thingsat/tinygs_2g4station/Firmware/Arduino/GroveTemperatureHumidity_TH02/README.md

# Grove Temperature&Humidity TH02

https://wiki.seeedstudio.com/Grove-TemptureAndHumidity_Sensor-High-Accuracy_AndMini-v1.0/

Step 1. Install the `Grove Temperature&Humidity TH02` library with `Tools > Manage Library ...`.

Step 2. Open, Build and Load the sketch `File > Examples > Grove Temper Humidity_TH02 > TH02_demo`

Step 3. Open the serial monitor with baudrate 9600 baud
