thingsat/tinygs_2g4station/Firmware/Arduino/RTC_DS1307/README.md

# RTC DS1307
https://www.arduino.cc/reference/en/libraries/ds1307rtc/
