thingsat/tinygs_2g4station/Firmware/Arduino/RTC_DS3231/README.md

# RTC DS3231
https://www.arduino.cc/reference/en/libraries/ds3231/
