thingsat/tinygs_2g4station/Firmware/Arduino/ADC_23_Click/README.md

# ADC 23 Click (MIKROE-5861)

https://www.mikroe.com/adc-23-click
