thingsat/tinygs_2g4station/Firmware/Arduino/ADC_8_Click/README.md

# ADC 8 Click (MIKROE-3394)

https://www.mikroe.com/adc-8-click

ADC 8 Click is a high precision, low-power, 16-bit analog-to-digital converter (ADC), based around the ADS1115 IC. It is capable of sampling signals on four single-ended or two differential input channels.
