thingsat/tinygs_2g4station/Firmware/Arduino/CAN/README.md

# CAN Bus

https://www.mikroe.com/click/interface/can
