thingsat/tinygs_2g4station/Firmware/Arduino/RS485_5_Click/README.md

# RS485 5 Click

The RS485 5 Click is a Click board™ equipped with the MAX485, low-power, slew-rate-limited transceiver for RS-485 and RS-422 communication, from Analog Devices. This device supports half-duplex RS-485 communication and can be used as an interface between the TTL level UART and the RS485 communication bus

https://www.mikroe.com/rs485-5-click
