thingsat/tinygs_2g4station/Firmware/Arduino/X-NUCLEO-IHM02A1/README.md

# X-NUCLEO-IHM02A1 Nucleo shield for driving steppers

https://www.st.com/en/ecosystems/x-nucleo-ihm02a1.html

Two axis stepper motor driver expansion board based on the L6470 for STM32 Nucleo
