thingsat/tinygs_2g4station/Firmware/Arduino/Grove_LCD_2x16/README.md

# Grove - LCD RGB Backlight

Connect a [Grove - LCD RGB screen](https://wiki.seeedstudio.com/Grove-LCD_RGB_Backlight/) on the I2C connector.

Download and install the [LCD lib](https://codeload.github.com/Seeed-Studio/Grove_LCD_RGB_Backlight/zip/refs/heads/master).

There are 12 examples for testing with the library.

Open `Scroll` in `File > Examples > Grove_LCD_RGB_Backlight-master`.
