thingsat/tinygs_2g4station/Firmware/Arduino/Analog_Input_Joystick/README.md

# Grove Thumb Joystick

Code for reading the 2 analog inputs of the Grove Thumb Joystick. 

This code can be used for controling manually the 2 steppers of the cubesat antenna tracker.

If you use the Board_Tinygs_2.4GHz_V1, the Grove Thumb Joystick can be directly connected to IN 34/35 grove connector.
