thingsat/tinygs_2g4station/Firmware/Arduino/GroveLoRaE5/README.md

# TinyGS 2G4 avec Grove LoRa E5

La platine [Grove LoRa E5](https://wiki.seeedstudio.com/Grove_LoRa_E5_New_Version) est un modem LoRaWAN basé sur le composant STM32WL55JC1. Le modem est commandable via des commandes AT (voir la [section Bonus](#Bonus)).

Il peut être branché sur la carte TinyGS 2G4 pour ajouter la connectivité LoRaWAN sur les bandes SubGHz (eu868, eu433 ...).

## Branchement

Le modem Grove LoRa E5 peut soit être branché 
* soit sur le connecteur Grove UART de la carte TinyGS
* soit être branché sur le header 2x19 de la carte TinyGS : Le fil blanc du cable Grove doit être branché sur la broche 17 du header 2x19 et le fil jaune du cable Grove doit être branché sur la broche 16.

## Sketch Arduino sur TinyGS 2G4

Ouvrez le Sketch [GroveLoRaE5.ino](GroveLoRaE5.ino)

Configurez les constantes dans le sketch
```c
#define DEBUG_AT 1
#define SEND_PERIOD 60000
#define REJOIN_PERIOD 60000
#define CONFIRMED 1
```

## Enregistrement

Repérez et relevez le `DevEUI`, l'`AppEUI` et l'`AppKey` de la [platine Grove LoRa E5](https://wiki.seeedstudio.com/Grove_LoRa_E5_New_Version/) dans la console série du enpoint.

Enregistrez le enpoint sur un réseau LoRaWAN ([TTN](https://console.cloud.thethings.network/), [Helium](https://console.helium.com/) ou Chirpstack) en utilisant le `DevEUI`, l'`AppEUI` et l'`AppKey` relevés.

> Vous pouvez changer les valeurs d'`AppEUI` et d'`AppKey` dans le croquis.

## Ajout d'une platine avec un capteur I2C

Vous pouvez améliorer le sketch en branchant une platine avec un capteur I2C sur le connecteur Grove I2C de la carte TinyGS

Ajoutez alors un décodeur adapté lors de l'enregistrement du enpoint sur le réseau LoRaWAN choisi.

Par exemple :

```javascript
function readInt16BE (buf, offset) {
    offset = offset >>> 0
    var val = buf[offset + 1] | (buf[offset] << 8)
    return (val & 0x8000) ? val | 0xFFFF0000 : val
  }

// For Helium et TTNv2
function Decode(fPort, bytes, variables) {
    var o = {};  
    o.temperature = readInt16BE(bytes,0);
    o.humidity = readInt16BE(bytes,2);
    // ...
    return o;
}

// For Helium et TTNv2
function Decoder(bytes, fPort) {
    return Decode(fPort, bytes, undefined);
}

// For  TTNv3 TODO

```

> Pour Helium, il faut [créer une nouvelle fonction](https://console.helium.com/functions).

Faites quelques tests pour changer les valeurs du capteur ...

Regardez les messages LoRaWAN envoyés par l'endpoint lorsque la procédure d'activation OTAA a réussi.

## Références

* https://wiki.seeedstudio.com/Grove_LoRa_E5_New_Version/
* https://files.seeedstudio.com/products/317990687/res/LoRa-E5%20AT%20Command%20Specification_V1.0%20.pdf

## Bonus

### Utilisation avec un adaptateur USB Série (aka FTDI) depuis un hôte Linux/MacOS/Windows

Branchez un cable Grove femelle sur l'adapteur USB Série (`RX` sur fil jaune, `TX` sur fil blanc).

Ouvrez une console série sur le prot série avec les paramêtres `9600 8N1`.

```
AT+ID                                                                   
+INFO: Input timeout                                                            
+ID: DevAddr, 32:30:A5:01                                                       
+ID: DevEui, 2C:F7:F1:20:12:23:34:45                                            
+ID: AppEui, 80:00:00:00:00:00:00:06                                            

AT+DR=EU868
+INFO: Input timeout                                                            
+DR: EU868                                                                      
                                                                                
AT+CH=NUM,0-2
+INFO: Input timeout                                                            
+CH: NUM, 0-2                                                                   

AT+KEY=APPKEY,2B7E151628AED2A6ABF7158809CF4F3C
+INFO: Input timeout                                                            
+KEY: APPKEY 2B7E151628AED2A6ABF7158809CF4F3C                                   

AT+MODE=LWOTAA
+INFO: Input timeout                                                            
+MODE: LWOTAA                                                                   
                                                                               
AT+CLASS=A
+INFO: Input timeout                                                            
+CLASS: A                                                                       
                                                                                
AT+PORT=8
+INFO: Input timeout                                                            
+PORT: 8                                                                        
                                                                                
AT+JOIN
+INFO: Input timeout                                                            
+JOIN: Start                                                                    
+JOIN: NORMAL                                                                   
+JOIN: Join failed                                                              
+JOIN: Done                                                                     
                                                                                
AT+JOIN
+INFO: Input timeout                                                            
+JOIN: Start                                                                    
+JOIN: NORMAL                                                                   
+JOIN: Network joined                                                           
+JOIN: NetID C0002B DevAddr FC:00:AC:2C                                         
+JOIN: Done                                                                     

AT+ID
+INFO: Input timeout                                                            
+ID: DevAddr, FC:00:AC:2C                                                       
+ID: DevEui, 2C:F7:F1:20:12:23:34:45                                            
+ID: AppEui, 80:00:00:00:00:00:00:06                                            

AT+CMSGHEX=2122232421222324
+INFO: Input timeout                                                            
+CMSGHEX: Start                                                                 
+CMSGHEX: Wait ACK                                                              
+CMSGHEX: FPENDING                                                              
+CMSGHEX: ACK Received                                                          
+CMSGHEX: RXWIN1, RSSI -72, SNR 6.0                                             
+CMSGHEX: Done                                                                  
                                                                                
AT+CMSGHEX=2122232421222324
+INFO: Input timeout                                                            
+CMSGHEX: Start                                                                 
+CMSGHEX: Wait ACK                                                              
+CMSGHEX: FPENDING                                                              
+CMSGHEX: ACK Received                                                          
+CMSGHEX: RXWIN1, RSSI -72, SNR 13.0                                            
+CMSGHEX: Done                                                                  

AT+DR
+INFO: Input timeout                                                            
+DR: DR0 (ADR DR5)                                                              
+DR: EU868 DR5  SF7  BW125K                                                     
+DR: EU868 DR0  SF12 BW125K                                                     
                                                                         
AT+ADR
+INFO: Input timeout                                                            
+ADR: ON                                                                        
                                                                                
AT+POWER
+INFO: Input timeout                                                            
+POWER: 12                                                                      
                                                                                
AT+VDD
+INFO: Input timeout                                                            
+VDD: 3.27V                                                                     
                                                                                
AT+WDT
+INFO: Input timeout                                                            
+WDT: ON                                                                        
                                                                                
AT+LOG
+INFO: Input timeout                                                            
+LOG: QUIET                                                                     

AT+LOG=DEBUG
+INFO: Input timeout                                                                                            
+LOG: DEBUG                                                                                                     
                                                                                
AT+CMSGHEX=2122232421222324
+INFO: Input timeout                                                            
+LOG: DEBUG                                                                     
+LOG: DEBUG   971961 LW      MACCMD, TX, 030706FF06                             
+LOG: DEBUG   971961 LW      MACCMD, RX, 0352FF0001                             
+LOG: DEBUG   971962 LW      ch 02                                              
+LOG: DEBUG   971962 LORA    RX, 868500000, SF7, 125KHz, 24                     
                                                                                
AT+CMSGHEX=2122232421222324
+INFO: Input timeout                                                            
+LOG:  WARN   988473 LW      tx 8, 2122232421222324(8)                          
+CMSGHEX: Start                                                                 
+CMSGHEX: Wait ACK                                                              
+LOG: DEBUG   988474 LW      MACCMD, TX, 0307                                   
+LOG: DEBUG   988474 LW      ch 00                                              
+LOG: DEBUG   988474 LORA    TX, 868100000, SF7, 125KHz, 8, 12                  
+LOG: DEBUG   988475 LORA    TX, 802CAC00FC82020003070897084ED874A8279461E7AFC3 
+LOG: DEBUG   989535 LORA    RX, 868100000, SF7, 125KHz, 24                     
+LOG: DEBUG   989594 LORA    RX, 602CAC00FCA502000354FF00012067D51D, -70, 14    
+LOG: DEBUG   989595 LW      MACCMD, RX, 0354FF0001                             
+CMSGHEX: FPENDING                                                              
+CMSGHEX: ACK Received                                                          
+CMSGHEX: RXWIN1, RSSI -70, SNR 14.0                                            
+CMSGHEX: Done

AT+CMSGHEX=2122232421222324
+INFO: Input timeout
+LOG:  WARN  1049959 LW      tx 8, 2122232421222324(8)
+CMSGHEX: Start
+CMSGHEX: Wait ACK
+LOG: DEBUG  1049960 LW      MACCMD, TX, 0307
+LOG: DEBUG  1049960 LW      ch 06
+LOG: DEBUG  1049960 LORA    TX, 867700000, SF7, 125KHz, 8, 8
+LOG: DEBUG  1049961 LORA    TX, 802CAC00FC8203000307082B4272553CA9F9726F527E7A
+LOG: DEBUG  1051021 LORA    RX, 867700000, SF7, 125KHz, 24
+LOG: DEBUG  1052062 LORA    RX, 869525000, SF12, 125KHz, 6
+LOG: DEBUG  1052975 LORA    TX, 867500000, SF7, 125KHz, 8, 8
+LOG: DEBUG  1052975 LORA    TX, 802CAC00FC8203000307082B4272553CA9F9726F527E7A
+LOG: DEBUG  1052976 LW      ch 05
+LOG: DEBUG  1054037 LORA    RX, 867500000, SF7, 125KHz, 24
+LOG: DEBUG  1055078 LORA    RX, 869525000, SF12, 125KHz, 6
+LOG: DEBUG  1055993 LORA    TX, 868100000, SF8, 125KHz, 8, 8
+LOG: DEBUG  1055993 LORA    TX, 802CAC00FC8203000307082B4272553CA9F9726F527E7A
+LOG: DEBUG  1055994 LW      ch 00
+LOG: DEBUG  1057109 LORA    RX, 868100000, SF8, 125KHz, 14
+LOG: DEBUG  1058147 LORA    RX, 869525000, SF12, 125KHz, 6
+CMSGHEX: Done

AT+JOIN
+INFO: Input timeout                                                                                            
+JOIN: Start                                                                                                    
+JOIN: NORMAL                                                                                                   
+LOG: DEBUG    87401 LW      ch 00                                                                              
+LOG: DEBUG    87401 LORA    TX, 868100000, SF12, 125KHz, 8, 14                                                 
+LOG: DEBUG    87402 LORA    TX, 00060000000000008001A5303220F1F72C51557AF69894                                 
+LOG: DEBUG    93924 LORA    RX, 868100000, SF12, 125KHz, 6                                                     
+LOG: DEBUG    95732 LORA    RX, 20F0237266D38BF423DE278F19E8F657695D02C0887D417D46DAB23FD20CC83A4B, -64, 6     
+JOIN: Network joined                                                                                           
+JOIN: NetID C0002B DevAddr FC:00:AE:C8                                                                         
+JOIN: Done                                                                                                     

```

```
AT+JOIN
+INFO: Input timeout                                                                                            
+JOIN: Start                                                                                                    
+JOIN: NORMAL                                                                                                   
+LOG: DEBUG    87401 LW      ch 00                                                                              
+LOG: DEBUG    87401 LORA    TX, 868100000, SF12, 125KHz, 8, 14                                                 
+LOG: DEBUG    87402 LORA    TX, 00060000000000008001A5303220F1F72C51557AF69894                                 
+LOG: DEBUG    93924 LORA    RX, 868100000, SF12, 125KHz, 6                                                     
+LOG: DEBUG    95732 LORA    RX, 20F0237266D38BF423DE278F19E8F657695D02C0887D417D46DAB23FD20CC83A4B, -64, 6     
+JOIN: Network joined                                                                                           
+JOIN: NetID C0002B DevAddr FC:00:AE:C8                                                                         
+JOIN: Done                                                                                                     
                                                                                                                
AT+CMSGHEX=2122232421222324
+INFO: Input timeout                                                                                            
+LOG:  WARN  2262881 LW      tx 8, 2122232421222324(8)                                                          
+CMSGHEX: Start                                                                                                 
+CMSGHEX: Wait ACK                                                                                              
+LOG: DEBUG  2262882 LW      ch 07                                                                              
+LOG: DEBUG  2262882 LORA    TX, 867900000, SF12, 125KHz, 8, 14                                                 
+LOG: DEBUG  2262882 LORA    TX, 80C8AE00FC800000089683D34295C5FE9B43D71E21                                     
+LOG: DEBUG  2265404 LORA    RX, 867900000, SF12, 125KHz, 6                                                     
+LOG: DEBUG  2266557 LW      MACCMD, RX, 06                                                                     
+LOG: DEBUG  2266557 LORA    RX, 60C8AE00FCA10000069985A409, -114, -7                                           
+CMSGHEX: FPENDING                                                                                              
+CMSGHEX: ACK Received                                                                                          
+CMSGHEX: RXWIN1, RSSI -114, SNR -8.0                                                                           
+CMSGHEX: Done                                                                                                  
```

Enqueue a downlink payload with port=10 and base64 encoded `SGVsbG8gV29ybGQ=` (`Hello World`) into the LNS web console.

```
AT+CMSGHEX=2122232421222324                                                                                            
+INFO: Input timeout                                                                                            
+LOG:  WARN  2281654 LW      tx 8, 2122232421222324(8)                                                          
+CMSGHEX: Start                                                                                                 
+CMSGHEX: Wait ACK                                                                                              
+LOG: DEBUG  2281655 LW      MACCMD, TX, 06FF38                                                                 
+LOG: DEBUG  2281655 LW      ch 06                                                                              
+LOG: DEBUG  2281655 LORA    TX, 867700000, SF12, 125KHz, 8, 14                                                 
+LOG: DEBUG  2281656 LORA    TX, 80C8AE00FC83010006FF3808BE54E0F1FD35132C17EF6947                               
+LOG: DEBUG  2284177 LORA    RX, 867700000, SF12, 125KHz, 6                                                     
+LOG: DEBUG  2285821 LORA    RX, A0C8AE00FCA501000310FF00010AD99E24FBF5F926F6CF444533B4D2BB, -114, -9           
+LOG: DEBUG  2285823 LW      MACCMD, RX, 0310FF0001                                                             
+CMSGHEX: FPENDING                                                                                              
+CMSGHEX: ACK Received                                                                                          
+CMSGHEX: PORT: 10; RX: "48656C6C6F20576F726C64"                                                                
+CMSGHEX: RXWIN1, RSSI -114, SNR -10.0                                                                          
+CMSGHEX: Done                                                                                                  
```

Disable ADR and set Datarate to 0 (long Range)
```
AT+ADR=OFF
+INFO: Input timeout                                                                                            
+ADR: OFF                                                                                                       
                                                                                                                
AT+DR=0
+INFO: Input timeout                                                                                            
+DR: DR0                                                                                                        
+DR: EU868 DR0  SF12 BW125K                                                                                     
```
