thingsat/tinygs_2g4station/images/board_v1.png

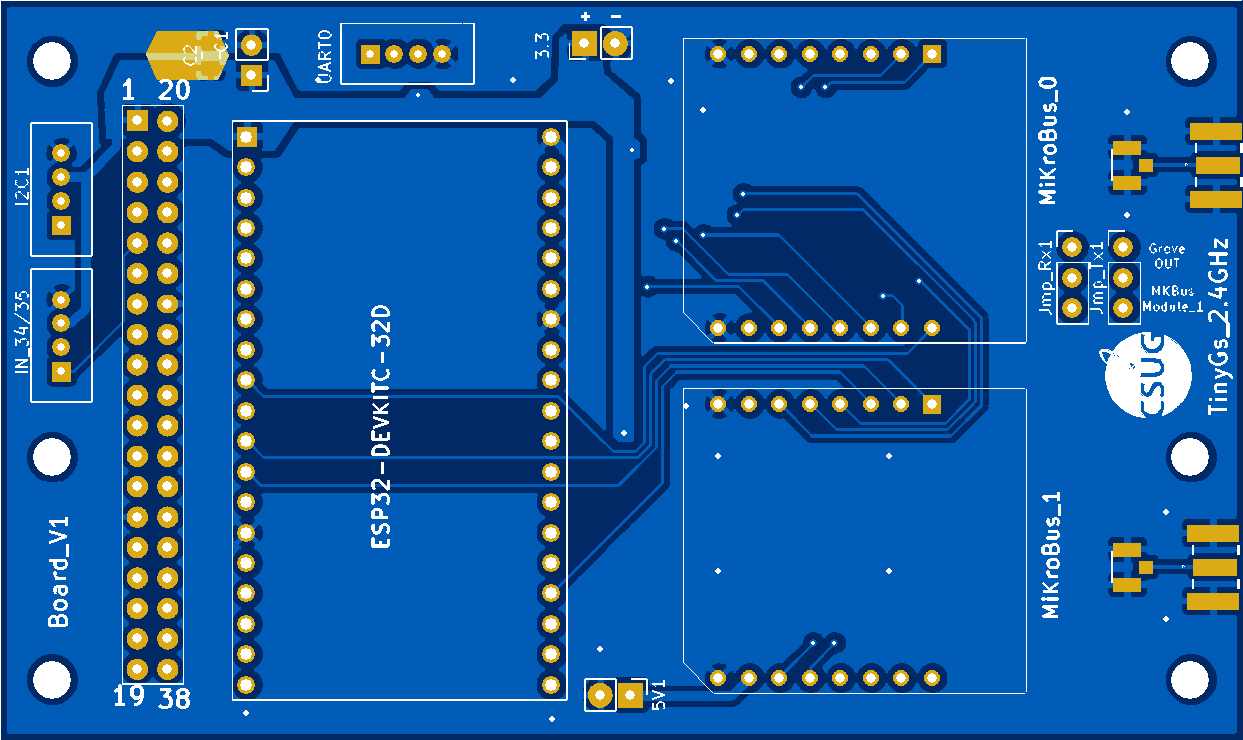
images/board_v1.png
