thingsat/tinygs_2g4station/images/ESP32-WROOM-32U-38pins.jpg

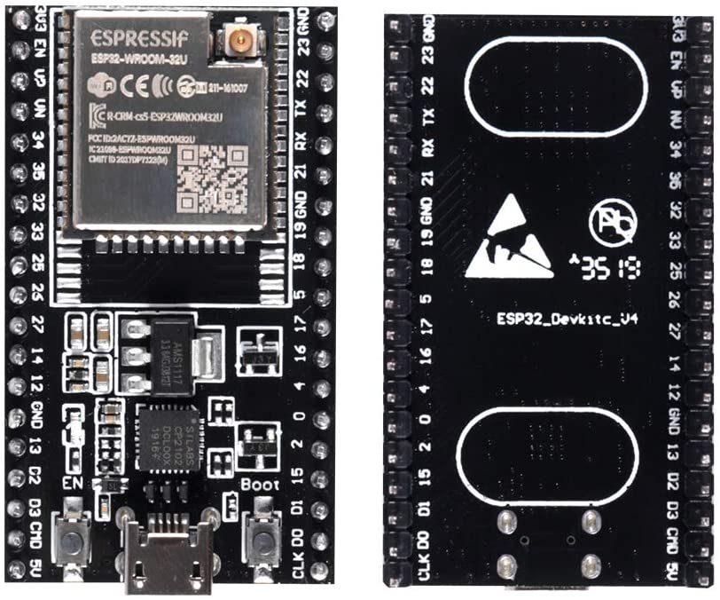
images/ESP32-WROOM-32U-38pins.jpg
