thingsat/tinygs_2g4station/images/gateway_tinygs_2g4-b.jpg

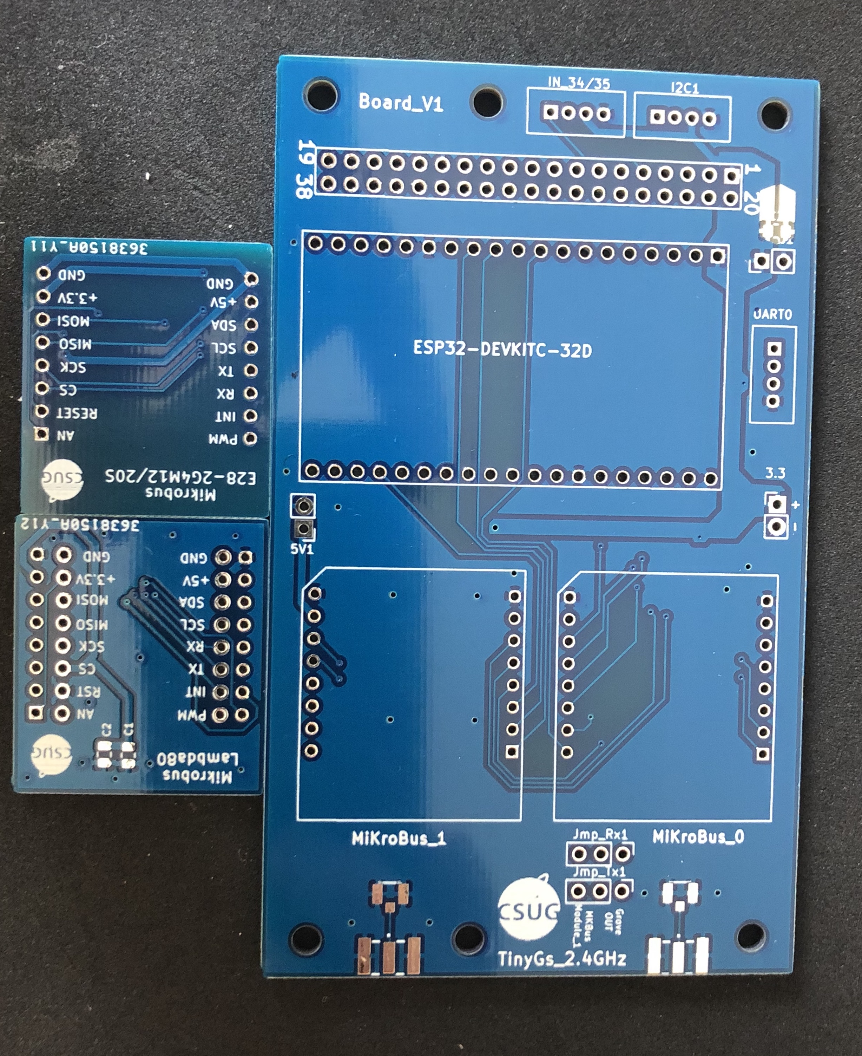
images/gateway_tinygs_2g4-b.jpg
