thingsat/tinygs_2g4station/images/mikrobus_e28.png

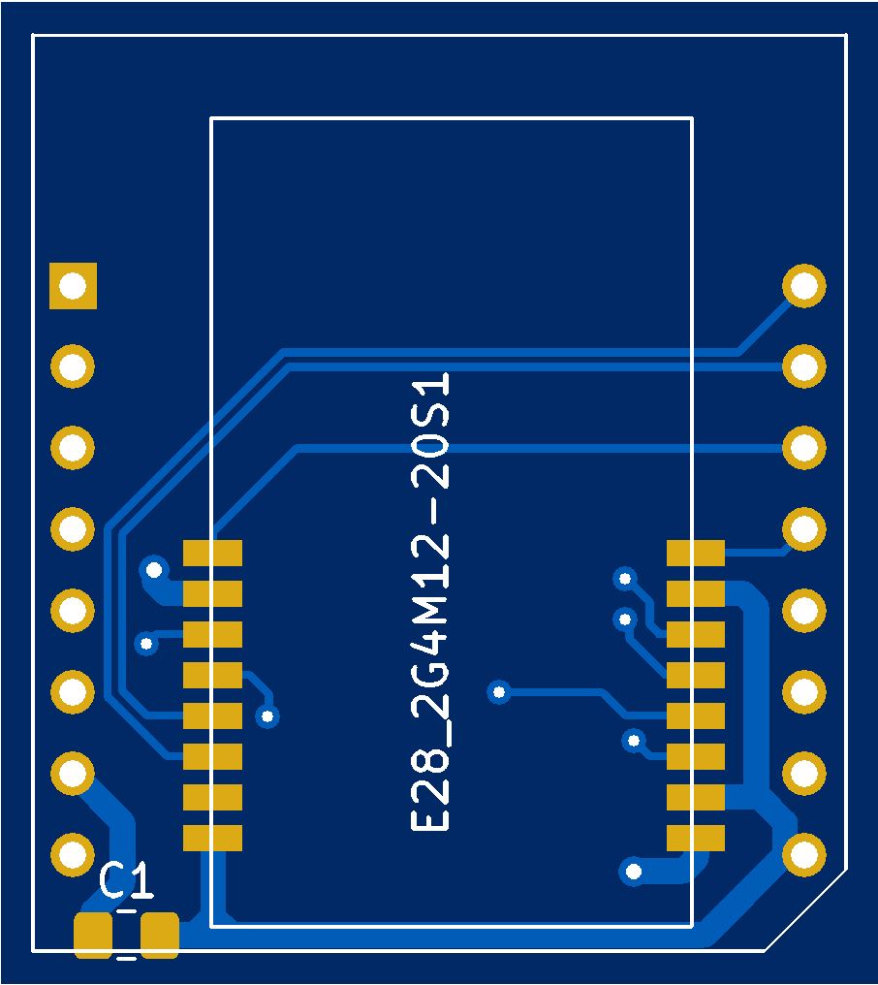
images/mikrobus_e28.png
