thingsat/tinygs_2g4station/images/mikrobus_lambda80.png

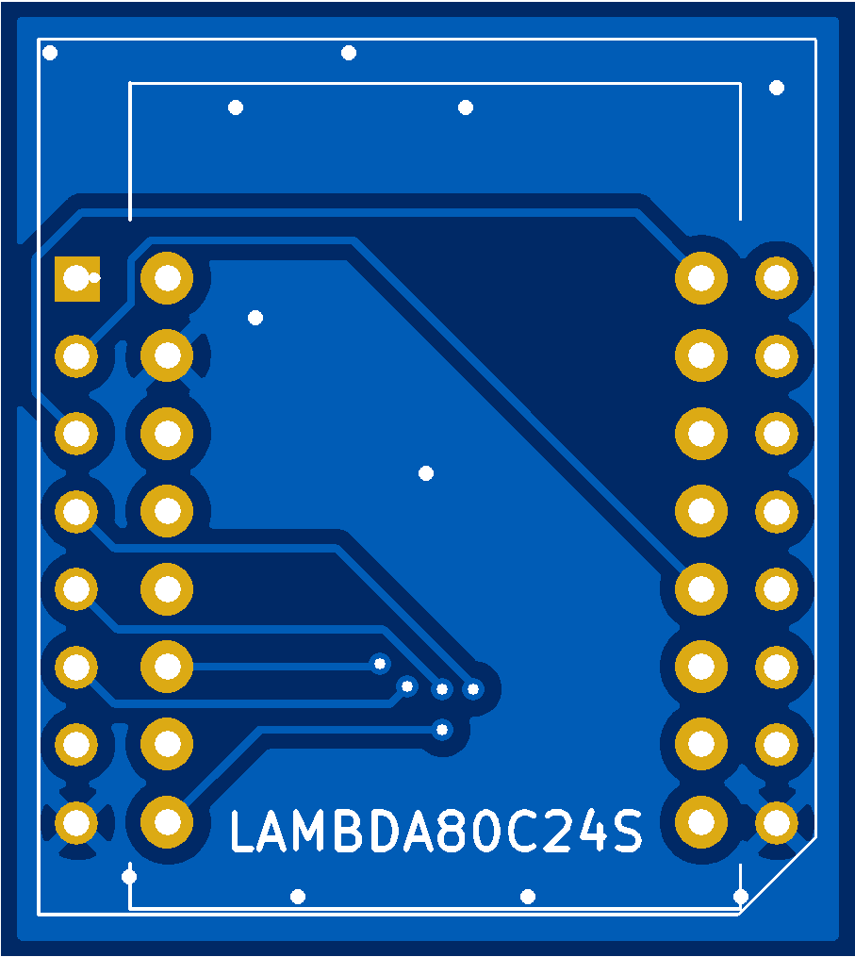
images/mikrobus_lambda80.png
