thingsat/tinygs_2g4station/Mikrobus_Board_EbyteE28/Picture/E28_Board_Bottom.PNG

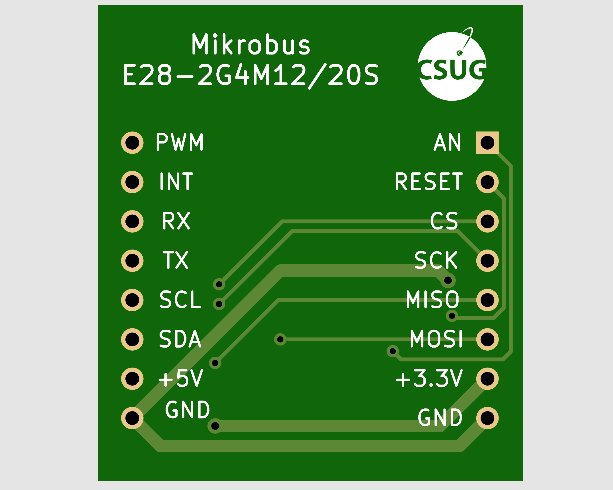
Mikrobus_Board_EbyteE28/Picture/E28_Board_Bottom.PNG
