thingsat/tinygs_2g4station/Mikrobus_Board_EbyteE28/Picture/E28_Board_Top.PNG

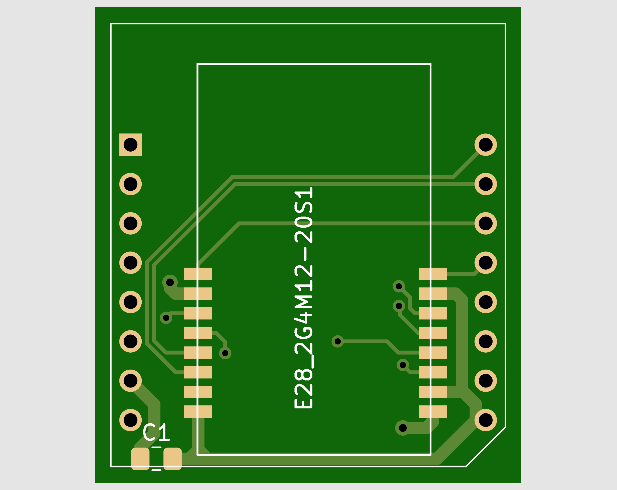
Mikrobus_Board_EbyteE28/Picture/E28_Board_Top.PNG
