thingsat/tinygs_2g4station/Mikrobus_Board_Lambda80C/Picture/Lamda80-24S.PNG

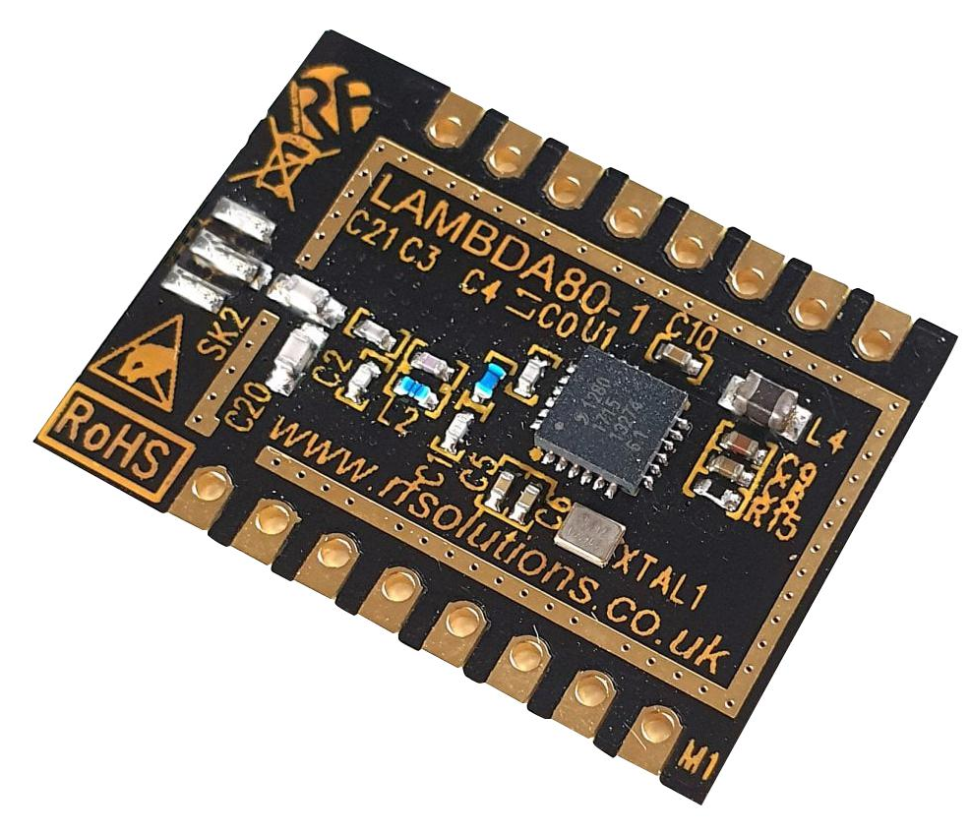
Mikrobus_Board_Lambda80C/Picture/Lamda80-24S.PNG
